richardhawthorn/mini_weather_panel/images/pcb_back.png

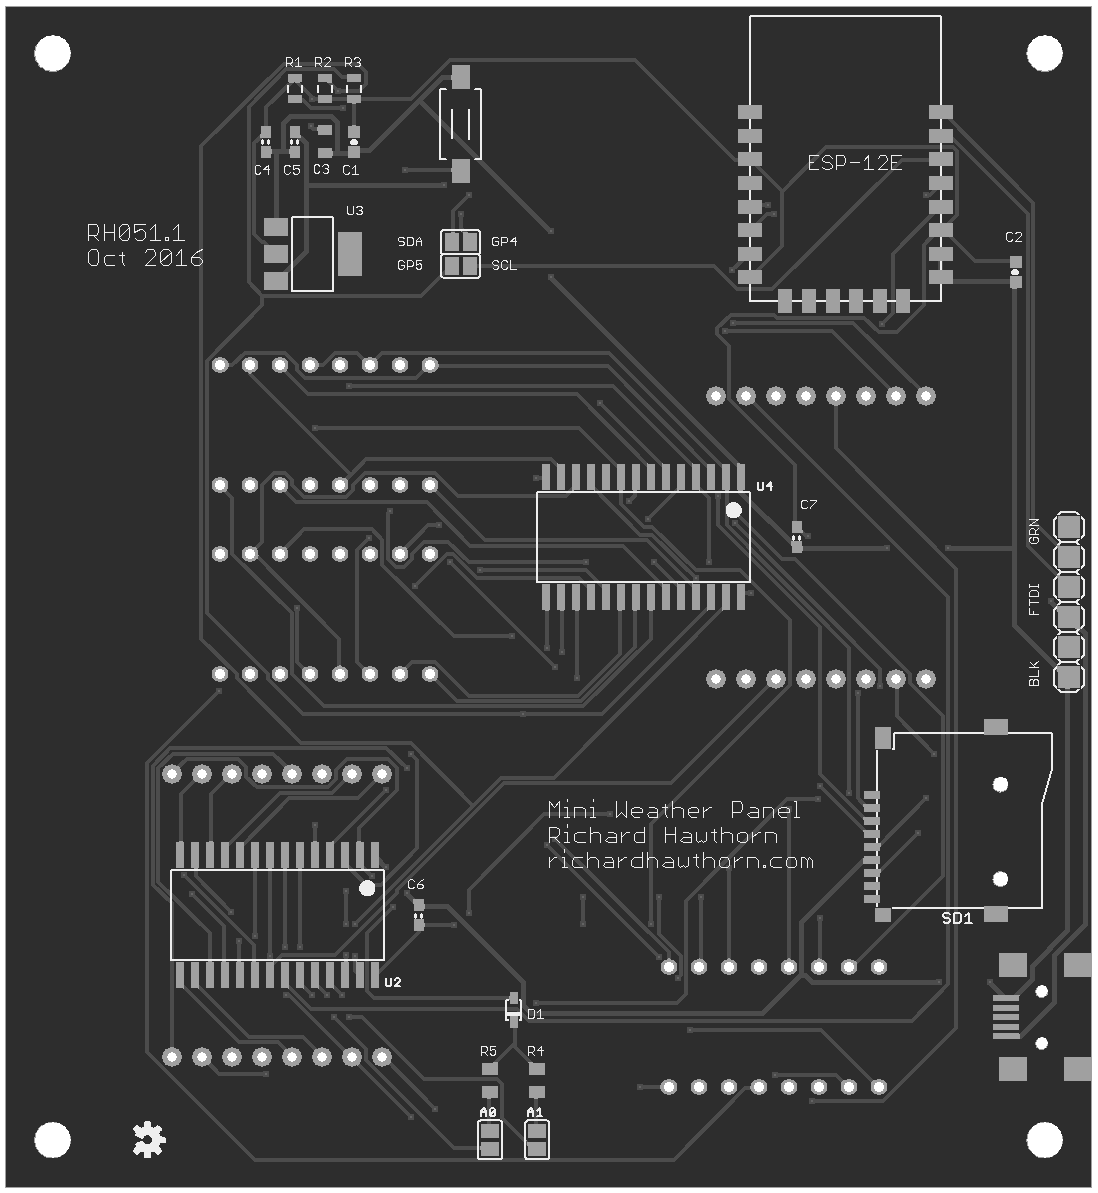
images/pcb_back.png
