richardhawthorn/mini_weather_panel/code/mini_weather_panel/variables.h

/*
 * Variables neede for the weather screen
 */
 
// *******************************************************
// *******************************************************

//Data from the SD card
String sd_ssid = "";
String sd_password = "";
String sd_apikey = "";
String sd_location = "";
String sd_units = "";
String sd_timezone = "";

//Data for the weather conditions
float current_temp;
float todays_temp;
int weather_icon;
int rainChart[8];

//Other settings
const char* host = "api.openweathermap.org";
int sleep_minutes = 1;

//Other variables
int lastkey = 0;
String json = "";
int connStep = 1;

// *******************************************************
// *******************************************************

//Weather icons
static const uint8_t
  conn1[] =
  { B00000000,
    B00000000,
    B00000000,
    B00010000,
    B00000000,
    B00000000,
    B00000000,
    B00000000 },
  conn2[] =
  { B00000000,
    B00000000,
    B00000000,
    B00001000,
    B00000000,
    B00000000,
    B00000000,
    B00000000 },
  conn3[] =
  { B00000000,
    B00000000,
    B00000000,
    B00000000,
    B00001000,
    B00000000,
    B00000000,
    B00000000 },
  conn4[] =
  { B00000000,
    B00000000,
    B00000000,
    B00000000,
    B00010000,
    B00000000,
    B00000000,
    B00000000 },
  ok[] =
  { B00000000,
    B00000000,
    B00000010,
    B00000100,
    B00001000,
    B01010000,
    B00100000,
    B00000000 },
  no[] =
  { B11101110,
    B10101010,
    B10101110,
    B00000000,
    B00000000,
    B00000000,
    B00000000,
    B00000000 },
  card[] =
  { B11100100,
    B10001010,
    B11100110,
    B00000000,
    B00000010,
    B11101110,
    B10001010,
    B10001110 },
  conf[] =
  { B11100100,
    B10001010,
    B11100100,
    B00000000,
    B00001110,
    B11101000,
    B10101100,
    B10101000 },
  conn[] =
  { B11100100,
    B10001010,
    B11100100,
    B00000000,
    B00000000,
    B11101110,
    B10101010,
    B10101010 },
  cloud[] =
  { B01110000,
    B10001110,
    B10000001,
    B10000001,
    B01111110,
    B00000000,
    B00000000,
    B00000000 },
  lightning[] =
  { B01110000,
    B10001110,
    B10000001,
    B10000001,
    B01111110,
    B00011000,
    B00110000,
    B00100000 },
  cloud_sun[] =
  { B01100011,
    B10111001,
    B10000100,
    B10000100,
    B01111000,
    B00000000,
    B00000000,
    B00000000 },
  cloud_sun_rain[] =
  { B01100011,
    B10111001,
    B10000100,
    B10000100,
    B01111000,
    B00000000,
    B00010000,
    B01000000 },
  cloud_rain[] =
  { B01110000,
    B10001110,
    B10000001,
    B10000001,
    B01111110,
    B00000000,
    B00001000,
    B00100000 },
  sun[] =
  { B10010001,
    B01000010,
    B00011000,
    B00111101,
    B10111100,
    B00011000,
    B01000010,
    B10001001 },
  mist[] =
  { B10101010,
    B01010101,
    B10101010,
    B01010101,
    B10101010,
    B01010101,
    B10101010,
    B01010101 },
  snow[] =
  { B00000000,
    B00010000,
    B00101000,
    B01010100,
    B00101000,
    B00010000,
    B00000000,
    B00000000 };

// *******************************************************
// *******************************************************
